kbx81/TubeClock/src/v1/Settings.h

//
// kbx81's tube clock settings class
// ---------------------------------------------------------------------------
// (c)2019 by kbx81. See LICENSE for details.
//
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
#pragma once

#include <cstdint>

#include "DateTime.h"

namespace kbxTubeClock {

class Settings {
 public:
  /// @brief Types of settings we keep
  ///
  enum Setting : uint8_t {
    SystemOptions = 0,
    BeepStates = 1,
    BlinkStates = 2,
    OnOffStates = 3,
    PMIndicatorRedValue = 4,
    PMIndicatorGreenValue = 5,
    PMIndicatorBlueValue = 6,
    TimeDisplayDuration = 7,
    DateDisplayDuration = 8,
    TemperatureDisplayDuration = 9,
    FadeDuration = 10,
    DstBeginMonth = 11,
    DstBeginDowOrdinal = 12,
    DstEndMonth = 13,
    DstEndDowOrdinal = 14,
    DstSwitchDayOfWeek = 15,
    DstSwitchHour = 16,
    EffectDuration = 17,
    EffectFrequency = 18,
    MinimumIntensity = 19,
    BeeperVolume = 20,
    TemperatureCalibrationSTM32 = 21,
    TemperatureCalibrationDS3234 = 22,
    TemperatureCalibrationDS1722 = 23,
    TemperatureCalibrationLM74 = 24,
    IdleTimeout = 25,
    DateFormat = 26,
    TimeZone = 27,
    ColonBehavior = 28,
    TimerResetValue = 29,
    DmxAddress = 30
  };

  /// @brief Settings we keep
  ///
  enum SystemOptionsBits : uint8_t {
    Display12Hour = 0,
    StatusLedAsAmPm = 1,
    HourlyChime = 2,
    DstEnable = 3,
    DisplayFahrenheit = 4,
    AutoAdjustIntensity = 5,
    StartupToToggle = 6,
    DmxExtended = 7,
    MSDsOff = 8,
    TriggerEffectOnRotate = 9
  };

  /// @brief Enums for time slots
  ///
  enum Slot : uint8_t {
    Slot1 = 0,
    Slot2 = 1,
    Slot3 = 2,
    Slot4 = 3,
    Slot5 = 4,
    Slot6 = 5,
    Slot7 = 6,
    Slot8 = 7,
    SlotDate = 8,
    SlotTemperature = 9,
    SlotTimer = 10,
    SlotMenu = 11,
    SlotSet = 12,
    SlotDmx = 13,
    SlotCalculated = 14
  };

 public:
  /// @brief Where settings will be written in FLASH
  /// @note This address is provided by the linker script (__settings_flash_start)
  ///       and is located at the end of flash memory to prevent conflicts with code
  ///
  static const uint32_t cSettingsFlashAddress;

  /// @brief How a setting's raw value is transformed for display/input
  ///
  enum class SettingTransform : uint8_t {
    None = 0,
    PlusOne,      ///< stored 0-based, displayed 1-based (e.g. DmxAddress: stored 0-504, shown 1-512)
    TimeZone,     ///< stored 0-112 (x15 min), displayed as signed ±HH:MM offset
    Calibration   ///< stored 0-198, displayed as signed offset from midpoint 99
  };

  /// @brief Describes valid range and display behavior of a setting
  ///
  struct SettingDescriptor {
    uint16_t        maxOrMask;   ///< max value for numerics; bitmask for bitfields
    uint8_t         minValue;    ///< minimum valid value (0 for most; 1 for months/ordinals)
    SettingTransform transform;  ///< how to interpret/display the value
  };

  /// @brief Descriptor for each setting (indexed by Setting enum)
  ///
  static const SettingDescriptor cSettingDescriptors[];

  /// @brief Midpoint value for signed temperature calibration encoding
  ///  stored = cCalibrationMidpoint + offsetCx10; offsetCx10 = stored - cCalibrationMidpoint
  static const int16_t cCalibrationMidpoint = 99;

  /// @brief Timezone encoding constants: stored value for UTC+0, and minutes per step
  ///  offsetMinutes = (stored - cTimeZoneUtcValue) * cTimeZoneStepMinutes
  static const uint16_t cTimeZoneUtcValue = 56;
  static const uint16_t cTimeZoneStepMinutes = 15;

  /// @brief Default constructor
  ///
  Settings();

  /// @brief Initialize settings
  ///
  void initialize();

  /// @brief Loads settings from FLASH
  /// @return true if success, false if failure & defaults were set
  ///
  bool loadFromFlash();

  /// @brief Loads settings from DS3234 SRAM; validates CRC
  /// @return true if DS3234 connected and CRC valid, false otherwise (defaults set)
  ///
  bool loadFromSram();

  /// @brief Saves current settings to DS3234 SRAM; no-op if DS3234 not connected
  /// @note Caller must ensure _crc is valid (i.e. call after saveToFlash())
  ///
  void saveToSram();

  /// @brief Invalidates the DS3234 SRAM copy of settings so it won't be used on next load; no-op if DS3234 not connected
  ///
  void invalidateSram();

  /// @brief Checks whether DS3234 SRAM contains valid settings (CRC check only, does not modify *this)
  /// @return true if DS3234 connected and SRAM CRC valid
  ///
  bool sramIsValid() const;

  /// @brief Saves settings to FLASH
  /// @return result of writeFlash()
  ///
  uint32_t saveToFlash();

  /// @brief Saves settings to FLASH only if they differ from the stored copy
  /// @return true on success (written or already up to date), false on write error
  ///
  bool saveToFlashIfChanged();

  /// @brief Returns a setting
  /// @return true if setting is enabled, false otherwise
  ///
  bool getSetting(const uint8_t setting, const uint8_t item);

  /// @brief Sets a setting
  ///
  void setSetting(const uint8_t setting, const uint8_t item, const bool state);

  /// @brief Returns all settings
  /// @return value of requested setting
  ///
  uint16_t getRawSetting(const uint8_t setting);

  /// @brief Sets all settings
  ///
  void setRawSetting(const uint8_t setting, const uint16_t value);

  /// @brief Get a time value stored in the settings
  ///
  DateTime getTime(const Slot setting);
  DateTime getTime(const uint8_t setting);

  /// @brief Set a time value in the settings
  ///
  void setTime(const Slot setting, const DateTime &time);
  void setTime(const uint8_t setting, const DateTime &time);

  /// @brief Returns the desired HV state based on the time
  /// @return true if HV should be on, false otherwise
  ///
  bool hvState();

 private:
  /// @brief array of values for various settings data
  ///
  uint16_t _setting[Setting::DmxAddress + 1];

  /// @brief array of stored times for the alarms and/or color changes
  ///
  DateTime _time[Slot::Slot8 + 1];

  /// @brief determines validity of Settings data after loading from FLASH
  ///
  uint32_t _crc;
};

}  // namespace kbxTubeClock
