kbx81/TubeClock/src/v1/Application.h

//
// kbx81's tube clock main application
// ---------------------------------------------------------------------------
// (c)2019 by kbx81. See LICENSE for details.
//
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
#pragma once

#include <cstdint>

#include "DateTime.h"
#include "Display.h"
#include "Settings.h"
#include "View.h"

namespace kbxTubeClock::Application {

/// @brief Application operating modes
///
enum OperatingMode : uint8_t {
  OperatingModeMainMenu,                  ///< Main Menu mode
  OperatingModeFixedDisplay,              ///< Fixed display mode
  OperatingModeToggleDisplay,             ///< Toggling display mode
  OperatingModeTimerCounter,              ///< Timer/counter mode
  OperatingModeDmx512Display,             ///< DMX-512 display mode
  OperatingModeSetClock,                  ///< Set timeclock mode
  OperatingModeSetDate,                   ///< Set date mode
  OperatingModeSetTimerResetValue,        ///< Set timer/counter reset value
  OperatingModeSystemStatusView,          ///< System status view mode
  OperatingModeSetSystemOptions,          ///< Set Binary/BCD and 24 hour bits mode
  OperatingModeSlotBeepConfig,            ///< Enable/Disable beeping (alarm) per-slot
  OperatingModeSlotBlinkConfig,           ///< Enable/Disable display blinking per-slot
  OperatingModeSlotOnOffConfig,           ///< Enable/Disable color change per-slot
  OperatingModeSlotPMIndicatorRGBConfig,  ///< Set RGB color for PM indicator
  OperatingModeSetDurationClock,          ///< Set duration of clock display mode
  OperatingModeSetDurationDate,           ///< Set duration of date display mode
  OperatingModeSetDurationTemp,           ///< Set duration of temperature display mode
  OperatingModeSetDurationFade,           ///< Set duration of fading for digits
  OperatingModeDstBeginMonth,             ///< Set first month of DST
  OperatingModeDstBeginDowOrdinal,        ///< Set which given day DST begins
  OperatingModeDstEndMonth,               ///< Set last month of DST
  OperatingModeDstEndDowOrdinal,          ///< Set which given day DST ends
  OperatingModeDstSwitchDayOfWeek,        ///< Set which day of week DST begins/ends
  OperatingModeDstSwitchHour,             ///< Set hour at which DST begins/ends
  OperatingModeSetEffectDuration,         ///< Set duration of display effects
  OperatingModeSetEffectFrequency,        ///< Set frequency of display effects
  OperatingModeSetMinimumIntensity,       ///< Set minimum display intensity
  OperatingModeSetBeeperVolume,           ///< Set Beeper Volume
  OperatingModeSetTempCalibration,        ///< Set temperature calibration
  OperatingModeSetIdleTimeout,            ///< Set idle timeout
  OperatingModeSetDateFormat,             ///< Set Date Format
  OperatingModeSetTimeZone,               ///< Set Time Zone
  OperatingModeSetColonBehavior,          ///< Set Colon/Seperator behavior (time display)
  OperatingModeSetDMX512Address,          ///< Set DMX-512 address mode
  OperatingModeSlot1Time,                 ///< Set slot 1 time mode
  OperatingModeSlot2Time,                 ///< Set slot 2 time mode
  OperatingModeSlot3Time,                 ///< Set slot 3 time mode
  OperatingModeSlot4Time,                 ///< Set slot 4 time mode
  OperatingModeSlot5Time,                 ///< Set slot 5 time mode
  OperatingModeSlot6Time,                 ///< Set slot 6 time mode
  OperatingModeSlot7Time,                 ///< Set slot 7 time mode
  OperatingModeSlot8Time,                 ///< Set slot 8 time mode
  OperatingModeTestDisplay                ///< Test display mode
};

/// @brief Enums for views
///
enum ViewEnum : uint8_t {
  MainMenuViewEnum = 0,
  TimeDateTempViewEnum = 1,
  TimerCounterViewEnum = 2,
  Dmx512ViewEnum = 3,
  SetTimeDateViewEnum = 4,
  SetBitsViewEnum = 5,
  SetValueViewEnum = 6,
  SystemStatusViewEnum = 7,
  TestDisplayEnum = 8
};

/// @brief Enums for views
///
enum ExternalControl : uint8_t { NoActiveExtControlEnum, SerialExtControlEnum, Dmx512ExtControlEnum };

/// @brief Number of seconds in a day
///
const uint16_t cSecondsInAnHour = 60 * 60;
const uint32_t cSecondsInADay = cSecondsInAnHour * 24;

// DST offset in seconds
//
static const int16_t cDstOffsetSeconds = 60 * 60;

/// @brief Common colors used throughout
///
extern const RgbLed red, green;

/// @brief Initialize the application
///
void initialize();

/// @brief Gets the application's date & time, adjusted for time zone and DST
///
DateTime dateTime();

/// @brief Set the date/time
///
void setDateTime(const DateTime &now);

/// @brief Returns the temperature based on hardware
///  (in fahrenheit if fahrenheit == true; in BCD if bcd == true)
int32_t temperature(const bool fahrenheit, const bool bcd = false);

/// @brief Returns the active sensor's temperature in tenths of degrees Celsius
///
int32_t temperatureCx10();

/// @brief Returns the temperature for a specific sensor type in tenths of degrees Celsius
///
int32_t temperatureCx10(Hardware::TempSensorType type);

/// @brief Returns true if any temperature reading has been updated since last call
///
bool temperatureUpdated();

/// @brief Get a mode's display number
/// @param mode Desired mode to get the display number for
///
uint8_t getModeDisplayNumber(OperatingMode mode);
uint8_t getModeDisplayNumber(uint8_t mode);

/// @brief Get application mode
///
OperatingMode getOperatingMode();

/// @brief Set new application mode
/// @param mode New application mode
///
void setOperatingMode(OperatingMode mode);

/// @brief Get view mode
///
ViewMode getViewMode();

/// @brief Set new view mode
/// @param mode New view mode
///
void setViewMode(ViewMode mode);

/// @brief Get view's related setting
/// @param mode Desired mode to get the related setting for
///
uint8_t getOperatingModeRelatedSetting(OperatingMode mode);

/// @brief Get external control status
///
ExternalControl getExternalControlState();

/// @brief Get a pointer to the application settings
///
Settings *getSettingsPtr();

/// @brief Refreshes hardware from current application settings
///
void refreshSettings();

/// @brief Notify the application that settings have been modified in-place via getSettingsPtr()
///
void notifySettingsChanged();

/// @brief Queue a serial notification that a numbered setting was changed via the local UI
/// @param settingNum The setting index that changed
///
void notifySettingChanged(uint8_t settingNum);

/// @brief Saves current settings to flash, skipping write if unchanged
/// @return true on success (saved or already up to date), false on write error
///
bool saveSettingsToFlash();

/// @brief Handles DST date/time computation; maintains clock's DST state machine.
///  Intended for tracking DST clock adjustments, not for arbitrary use!
///  To reset state machine, call with year != year provided when last called.
/// @param currentTime DateTime object to compute DST state for
/// @return true if DST is active based on passed DateTime object
bool isDst(const DateTime &currentTime);

/// @brief Returns state of automatic tube intensity adjustments
/// @return True if automatic tube intensity adjustment is enabled
bool getIntensityAutoAdjust();

/// @brief Enables/disables automatic adjusting of the tube display intensity based
///  on ambient light seen by the phototransistor
/// @param enable Enables automatic adjustments if true
/// @param quickAdjust Perform an immediate update of the intensity
void setIntensityAutoAdjust(const bool enable, const bool quickAdjust = false);

/// @brief Returns state of automatic status LED intensity adjustments
/// @return True if automatic LED intensity adjustment is enabled
bool getLedIntensityAutoAdjust();

/// @brief Enables/disables automatic adjusting of the status LED intensity based
///  on ambient light. Independent of tube auto-adjust.
/// @param enable Enables automatic LED adjustments if true
void setLedIntensityAutoAdjust(const bool enable);

/// @brief Returns the application's current display intensity
/// @return current display intensity (0-255)
uint8_t getIntensity();

/// @brief Returns the status LED's current master intensity
/// @return current LED intensity (0-255)
uint8_t getLedIntensity();

/// @brief Returns the application's startup settings load result
/// @return 0 = defaults used, 1 = loaded from flash, 2 = loaded from DS3234 SRAM
uint8_t getStartupSettingsLoadResult();

/// @brief Set the application's display intensity and disables automagic adjusting of the display intensity
/// @param intensity New display intensity (0-255)
///
void setIntensity(const uint8_t intensity);

/// @brief Set the status LED's master intensity independently of the nixie display intensity.
///        Disables LED auto-adjust; tube auto-adjust is unaffected.
/// @param intensity New LED intensity (0-255)
///
void setLedIntensity(const uint8_t intensity);

/// @brief Refreshs master display intensity. Call at fixed intervals.
///
void tick();

/// @brief The main loop of the application.
///
__attribute__((noreturn)) void loop();

}  // namespace kbxTubeClock::Application
