kbx81/TubeClock/src/v1/RgbLed.cpp

//
// kbx81's RGB LED Library
// ---------------------------------------------------------------------------
// (c)2017 by kbx81. See LICENSE for details.
//
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

#include "RgbLed.h"

/// @mainpage
///
/// @section intro_sec Introduction
///
/// This library contains a class to manage the Binary Clock's RGB LEDs.
///
/// @section requirements_sec Requirements
///
/// This library is written in a manner so as to be compatible on a range of
/// CPUs/MCUs. It has been tested on Arduino and STM32F0 platforms. It requires
/// a modern C++ compiler (C++11).
///
/// @section classes_sec Classes
///
/// There is only the RgbLed::RgbLed class. Read the documentation of this class
/// for all details.
///

namespace kbxTubeClock {

/// 4096-step (12 bit) brightness table: gamma = 2.2
///
const uint16_t RgbLed::cGammaTable[4096] = {
    0,    0,    0,    0,    0,    0,    0,    0,    0,    0,    0,    0,    0,    0,    0,    0,    0,    0,    0,
    0,    0,    0,    0,    0,    0,    0,    0,    0,    0,    0,    0,    0,    0,    0,    0,    0,    0,    0,
    0,    0,    0,    0,    0,    0,    0,    0,    0,    0,    0,    0,    0,    0,    0,    0,    0,    0,    0,
    0,    0,    0,    0,    0,    0,    0,    0,    0,    0,    0,    1,    1,    1,    1,    1,    1,    1,    1,
    1,    1,    1,    1,    1,    1,    1,    1,    1,    1,    1,    1,    1,    1,    1,    1,    1,    1,    1,
    1,    1,    1,    1,    1,    1,    1,    1,    1,    1,    1,    1,    1,    1,    1,    1,    1,    1,    2,
    2,    2,    2,    2,    2,    2,    2,    2,    2,    2,    2,    2,    2,    2,    2,    2,    2,    2,    2,
    2,    2,    2,    2,    2,    2,    2,    2,    2,    3,    3,    3,    3,    3,    3,    3,    3,    3,    3,
    3,    3,    3,    3,    3,    3,    3,    3,    3,    3,    3,    3,    3,    3,    4,    4,    4,    4,    4,
    4,    4,    4,    4,    4,    4,    4,    4,    4,    4,    4,    4,    4,    4,    4,    5,    5,    5,    5,
    5,    5,    5,    5,    5,    5,    5,    5,    5,    5,    5,    5,    5,    6,    6,    6,    6,    6,    6,
    6,    6,    6,    6,    6,    6,    6,    6,    6,    6,    7,    7,    7,    7,    7,    7,    7,    7,    7,
    7,    7,    7,    7,    7,    7,    8,    8,    8,    8,    8,    8,    8,    8,    8,    8,    8,    8,    8,
    8,    9,    9,    9,    9,    9,    9,    9,    9,    9,    9,    9,    9,    10,   10,   10,   10,   10,   10,
    10,   10,   10,   10,   10,   10,   11,   11,   11,   11,   11,   11,   11,   11,   11,   11,   11,   11,   12,
    12,   12,   12,   12,   12,   12,   12,   12,   12,   12,   13,   13,   13,   13,   13,   13,   13,   13,   13,
    13,   14,   14,   14,   14,   14,   14,   14,   14,   14,   14,   15,   15,   15,   15,   15,   15,   15,   15,
    15,   15,   16,   16,   16,   16,   16,   16,   16,   16,   16,   17,   17,   17,   17,   17,   17,   17,   17,
    17,   17,   18,   18,   18,   18,   18,   18,   18,   18,   19,   19,   19,   19,   19,   19,   19,   19,   19,
    20,   20,   20,   20,   20,   20,   20,   20,   21,   21,   21,   21,   21,   21,   21,   21,   22,   22,   22,
    22,   22,   22,   22,   22,   23,   23,   23,   23,   23,   23,   23,   23,   24,   24,   24,   24,   24,   24,
    24,   25,   25,   25,   25,   25,   25,   25,   25,   26,   26,   26,   26,   26,   26,   26,   27,   27,   27,
    27,   27,   27,   27,   28,   28,   28,   28,   28,   28,   28,   29,   29,   29,   29,   29,   29,   30,   30,
    30,   30,   30,   30,   30,   31,   31,   31,   31,   31,   31,   31,   32,   32,   32,   32,   32,   32,   33,
    33,   33,   33,   33,   33,   34,   34,   34,   34,   34,   34,   34,   35,   35,   35,   35,   35,   35,   36,
    36,   36,   36,   36,   36,   37,   37,   37,   37,   37,   37,   38,   38,   38,   38,   38,   39,   39,   39,
    39,   39,   39,   40,   40,   40,   40,   40,   40,   41,   41,   41,   41,   41,   42,   42,   42,   42,   42,
    42,   43,   43,   43,   43,   43,   44,   44,   44,   44,   44,   44,   45,   45,   45,   45,   45,   46,   46,
    46,   46,   46,   47,   47,   47,   47,   47,   47,   48,   48,   48,   48,   48,   49,   49,   49,   49,   49,
    50,   50,   50,   50,   50,   51,   51,   51,   51,   51,   52,   52,   52,   52,   52,   53,   53,   53,   53,
    53,   54,   54,   54,   54,   55,   55,   55,   55,   55,   56,   56,   56,   56,   56,   57,   57,   57,   57,
    57,   58,   58,   58,   58,   59,   59,   59,   59,   59,   60,   60,   60,   60,   61,   61,   61,   61,   61,
    62,   62,   62,   62,   63,   63,   63,   63,   63,   64,   64,   64,   64,   65,   65,   65,   65,   65,   66,
    66,   66,   66,   67,   67,   67,   67,   68,   68,   68,   68,   69,   69,   69,   69,   69,   70,   70,   70,
    70,   71,   71,   71,   71,   72,   72,   72,   72,   73,   73,   73,   73,   74,   74,   74,   74,   75,   75,
    75,   75,   76,   76,   76,   76,   77,   77,   77,   77,   78,   78,   78,   78,   79,   79,   79,   79,   80,
    80,   80,   80,   81,   81,   81,   81,   82,   82,   82,   82,   83,   83,   83,   84,   84,   84,   84,   85,
    85,   85,   85,   86,   86,   86,   86,   87,   87,   87,   88,   88,   88,   88,   89,   89,   89,   89,   90,
    90,   90,   91,   91,   91,   91,   92,   92,   92,   92,   93,   93,   93,   94,   94,   94,   94,   95,   95,
    95,   96,   96,   96,   96,   97,   97,   97,   98,   98,   98,   98,   99,   99,   99,   100,  100,  100,  100,
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

RgbLed::RgbLed(const uint16_t red, const uint16_t green, const uint16_t blue, const uint32_t duration)
    : _duration(duration), _red(red), _green(green), _blue(blue) {}

bool RgbLed::operator==(const RgbLed &other) const {
  return _red == other._red && _green == other._green && _blue == other._blue && _duration == other._duration &&
         _intensity == other._intensity;
}

bool RgbLed::operator!=(const RgbLed &other) const { return !(*this == other); }

void RgbLed::setIntensity(const uint8_t intensity) { _intensity = intensity; }

void RgbLed::setRed(const uint16_t intensityRed) { _red = intensityRed; }

void RgbLed::setGreen(const uint16_t intensityGreen) { _green = intensityGreen; }

void RgbLed::setBlue(const uint16_t intensityBlue) { _blue = intensityBlue; }

void RgbLed::setRGB(const uint16_t intensityRed, const uint16_t intensityGreen, const uint16_t intensityBlue) {
  _red = intensityRed;
  _green = intensityGreen;
  _blue = intensityBlue;
}

void RgbLed::setOff() {
  _red = 0;
  _green = 0;
  _blue = 0;
}

void RgbLed::setDuration(const uint32_t duration) { _duration = duration; }

uint8_t RgbLed::getIntensity() const { return _intensity; }

uint16_t RgbLed::getRed() const { return _red; }

uint16_t RgbLed::getGreen() const { return _green; }

uint16_t RgbLed::getBlue() const { return _blue; }

uint32_t RgbLed::getDuration() const { return _duration; }

void RgbLed::adjustIntensity(uint16_t scaleFactor) {
  uint32_t top;

  top = _red * scaleFactor;
  _red = top >> 16;

  top = _green * scaleFactor;
  _green = top >> 16;

  top = _blue * scaleFactor;
  _blue = top >> 16;
}

void RgbLed::gammaCorrect12bit() {
  const uint16_t mask = 0xfff;  // 12 bits

  _red = RgbLed::cGammaTable[_red & mask];
  _green = RgbLed::cGammaTable[_green & mask];
  _blue = RgbLed::cGammaTable[_blue & mask];
}

}  // namespace kbxTubeClock
