kbx81/TubeClock/src/v1/GpsReceiver.cpp

//
// kbx81's tube clock GpsReceiver Library
// ---------------------------------------------------------------------------
// (c)2019 by kbx81. See LICENSE for details.
//
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
#include <cstring>

#include "Hardware.h"
#include "GpsReceiver.h"

#if HARDWARE_VERSION == 1
#include "Hardware_v1.h"
#else
#error HARDWARE_VERSION must be defined with a value of 1
#endif

namespace kbxTubeClock::GpsReceiver {

/// @brief GPS Receiver state machine states
///
enum GpsRxState : uint8_t {
  GpsRxIdle = 0,
  GpsRxGettingHeader = 1,
  GpsRxNmeaHeaderValid = 2,
  GpsRxTimeReceived = 3,
  GpsRxTimeCompleted = 4,
  GpsRxWaitForDate = 5,
  GpsRxDate = 6,
  GpsRxNumSatellites = 7,
  GpsRxWaitForChecksum = 8,  // GPRMC: eat trailing fields until '*'
  GpsRxChecksumHigh = 9,     // read high hex nibble of checksum
  GpsRxChecksumLow = 10      // read low hex nibble, validate, commit
};

/// @brief GPS Receiver sentence type
///
enum GpsRxType : uint8_t { GpsRMC = 0, GpsGSV = 1 };

// the header on the string we expect to parse
// $GPRMC,000012.800,V,,,,,0.00,0.00,060180,,,N*49
// $GPRMC,230912.000,A,4055.5342,N,08341.7690,W,1.24,299.67,070519,,,D*71
//
static const char cGpsParseStrGSV[] = "$GPGSV,";
static const char cGpsParseStrRMC[] = "$GPRMC,";

// the length of the string we expect to parse
//
static const uint8_t cGpsNmeaHeaderLength = 7;

// the length of the date and time strings we expect to receive
//
static const uint8_t cGpsDateTimeLength = 6;

// the number of commas seen before we receive the date
//
static const uint8_t cGpsPreDateCommaCount = 7;

// the number of commas seen before we receive the number of satellites
//
static const uint8_t cGpsPreNumSatellitesCommaCount = 2;

// tracks the receiver state machine's state
//
static GpsRxState _rxState = GpsRxState::GpsRxIdle;

// tracks the sentence type the receiver is sending
//
static GpsRxType _rxType = GpsRxType::GpsRMC;

// a counter for incoming characters
//
static uint8_t _rxCharCount = 0;

// indicates the validity of the incoming data
//
static char _rxValidChar = 0;

// buffer for sentence header (7 bytes, .bss — init value irrelevant, ISR overwrites all bytes)
//
static char _rxHeaderChar[7];

// date and time incoming character buffers
//
static char _rxDateChar[6];
static char _rxTimeChar[6];

// number of  minutes added to GPS time to compute local time
//
static int16_t _timeZoneOffsetInMinutes = 0;

// the current date and time received from the GPS
//
static DateTime _gpsTime;

// the current number of satellites seen by the GPS
//
static uint8_t _numSatellites = 0;

// NMEA checksum state: running XOR accumulator and received checksum byte
//
static uint8_t _checksum = 0;
static uint8_t _checksumRx = 0;

// cached Usart pointer for GPS USART
//
static Usart *_gpsUsart = nullptr;

// Decode one ASCII hex character to its 4-bit value
//
static uint8_t _hexNibble(const uint8_t c) {
  return (c >= 'A') ? (c - 'A' + 10) : (c - '0');
}

void initialize() {
  _gpsUsart = Hardware::getUsart(0);  // USART1
}

/// @brief Updates our DateTime object based on the receive buffers
///
void _rxRmcComplete() {
  uint16_t year = 2000;
  uint8_t month = 0, day = 0, hour = 0, minute = 0, second = 0;

  day = ((_rxDateChar[0] - '0') * 10) + (_rxDateChar[1] - '0');
  month = ((_rxDateChar[2] - '0') * 10) + (_rxDateChar[3] - '0');
  year += ((_rxDateChar[4] - '0') * 10) + (_rxDateChar[5] - '0');

  hour = ((_rxTimeChar[0] - '0') * 10) + (_rxTimeChar[1] - '0');
  minute = ((_rxTimeChar[2] - '0') * 10) + (_rxTimeChar[3] - '0');
  second = ((_rxTimeChar[4] - '0') * 10) + (_rxTimeChar[5] - '0');

  _gpsTime.setDate(year, month, day);
  _gpsTime.setTime(hour, minute, second);
}

bool isConnected() { return ((_rxValidChar == 'A') || (_rxValidChar == 'V')); }

bool isValid() { return (_rxValidChar == 'A'); }

DateTime getDateTime() { return _gpsTime; }

DateTime getLocalDateTime() { return _gpsTime.addSeconds(_timeZoneOffsetInMinutes * 60); }

uint8_t getSatellitesInView() { return _numSatellites; }

void setTimeZone(const int16_t offsetInMinutes) { _timeZoneOffsetInMinutes = offsetInMinutes; }

void rxIsr() {
  if (_gpsUsart == nullptr || !_gpsUsart->rxReady()) {
    return;
  }

  uint8_t rxChar = _gpsUsart->readByte();

  // Accumulate XOR checksum for all bytes between '$' (exclusive) and '*' (exclusive).
  // States GpsRxGettingHeader through GpsRxDate cover the header + all RMC payload fields.
  // GpsRxWaitForChecksum handles bytes between the date field and '*' inline.
  if (_rxState >= GpsRxState::GpsRxGettingHeader && _rxState <= GpsRxState::GpsRxDate) {
    _checksum ^= rxChar;
  }

  switch (_rxState) {
    // at this point, we've seen the "$GPRMC," characters and can expect the time or a sentence count next
    case GpsRxState::GpsRxNmeaHeaderValid:
      if (_rxType == GpsRxType::GpsRMC) {
        _rxTimeChar[_rxCharCount] = rxChar;

        if (++_rxCharCount >= cGpsDateTimeLength) {
          _rxState = GpsRxState::GpsRxTimeReceived;
          _rxCharCount = 0;
        }
      } else if (_rxType == GpsRxType::GpsGSV) {
        if (rxChar == ',') {
          if (++_rxCharCount >= cGpsPreNumSatellitesCommaCount) {
            _rxState = GpsRxState::GpsRxNumSatellites;
            _rxCharCount = 0;
          }
        }
      }
      break;

    // the time has been received, here we'll just eat a comma and move along
    case GpsRxState::GpsRxTimeReceived:
      if (rxChar == ',') {
        _rxState = GpsRxState::GpsRxTimeCompleted;
      }
      break;

    // now we should see either an 'A' or a 'V' indicating validity
    case GpsRxState::GpsRxTimeCompleted:
      if ((rxChar == 'A') || (rxChar == 'V')) {
        _rxValidChar = rxChar;
        _rxState = GpsRxState::GpsRxWaitForDate;
      } else {
        _rxState = GpsRxState::GpsRxIdle;
      }
      break;

    // the validity has been received, now we'll eat more commas
    case GpsRxState::GpsRxWaitForDate:
      if (rxChar == ',') {
        if (++_rxCharCount >= cGpsPreDateCommaCount) {
          _rxState = GpsRxState::GpsRxDate;
          _rxCharCount = 0;
        }
      }
      break;

    // finally we get the date; defer commit until checksum validates
    case GpsRxState::GpsRxDate:
      _rxDateChar[_rxCharCount] = rxChar;

      if (++_rxCharCount >= cGpsDateTimeLength) {
        _rxState = GpsRxState::GpsRxWaitForChecksum;
        _rxCharCount = 0;
      }
      break;

    // eat trailing GPRMC fields until '*', accumulating them into the checksum
    case GpsRxState::GpsRxWaitForChecksum:
      if (rxChar == '*') {
        _rxState = GpsRxState::GpsRxChecksumHigh;
      } else {
        _checksum ^= rxChar;
      }
      break;

    // read high hex nibble of received checksum
    case GpsRxState::GpsRxChecksumHigh:
      _checksumRx = _hexNibble(rxChar) << 4;
      _rxState = GpsRxState::GpsRxChecksumLow;
      break;

    // read low hex nibble, validate, and commit if checksum matches
    case GpsRxState::GpsRxChecksumLow:
      _checksumRx |= _hexNibble(rxChar);
      if (_checksumRx == _checksum) {
        _rxRmcComplete();
      }
      _rxState = GpsRxState::GpsRxIdle;
      _rxCharCount = 0;
      break;

    // read in the two-digit number of satellites — accumulate directly to avoid buffer
    case GpsRxState::GpsRxNumSatellites:
      if (_rxCharCount == 0) {
        _numSatellites = (rxChar - '0') * 10;
        ++_rxCharCount;
      } else {
        _numSatellites += rxChar - '0';
        _rxState = GpsRxState::GpsRxIdle;
        _rxCharCount = 0;
      }
      break;

    // the first big step...read in up to cGpsNmeaHeaderLength header characters
    case GpsRxState::GpsRxGettingHeader:
      _rxHeaderChar[_rxCharCount] = rxChar;
      // if we've received enough characters, compare the strings for validity
      if (++_rxCharCount >= cGpsNmeaHeaderLength) {
        if (memcmp(cGpsParseStrGSV, _rxHeaderChar, cGpsNmeaHeaderLength) == 0) {
          _rxState = GpsRxState::GpsRxNmeaHeaderValid;
          _rxType = GpsRxType::GpsGSV;
          _rxCharCount = 0;
        } else if (memcmp(cGpsParseStrRMC, _rxHeaderChar, cGpsNmeaHeaderLength) == 0) {
          _rxState = GpsRxState::GpsRxNmeaHeaderValid;
          _rxType = GpsRxType::GpsRMC;
          _rxCharCount = 0;
        } else  // nothing matched so just start over
        {
          _rxState = GpsRxState::GpsRxIdle;
          _rxCharCount = 0;
        }
      }
      break;

    // it starts here...we patiently wait for that money header tag! ('$')
    default:
      if (rxChar == '$') {
        _checksum = 0;  // reset XOR accumulator for new sentence ('$' itself is not checksummed)
        _rxHeaderChar[_rxCharCount++] = rxChar;
        _rxState = GpsRxState::GpsRxGettingHeader;
      }
  }
}

}  // namespace kbxTubeClock::GpsReceiver
