kbx81/TubeClock/src/v1/SystemStatusView.cpp

//
// kbx81's tube clock system status view class
// ---------------------------------------------------------------------------
// (c)2019 by kbx81. See LICENSE for details.
//
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
#include "Application.h"
#include "BuildInfo.h"
#include "DateTime.h"
#include "DisplayManager.h"
#include "GpsReceiver.h"
#include "Hardware.h"
#include "Settings.h"
#include "SystemStatusView.h"

#if HARDWARE_VERSION == 1
#include "Hardware_v1.h"
#else
#error HARDWARE_VERSION must be defined with a value of 1
#endif

namespace kbxTubeClock {

SystemStatusView::SystemStatusView() : _selectedView(0) {}

void SystemStatusView::enter(const Settings::SettingDescriptor * /*descriptor*/, uint8_t /*relatedSetting*/,
                             uint8_t /*numSettings*/) {
  DisplayManager::setStatusLedAutoRefreshing(true);
}

bool SystemStatusView::keyHandler(Keys::Key key) {
  bool tick = false;

  if (key == Keys::Key::A) {
  }

  if (key == Keys::Key::B) {
  }

  if (key == Keys::Key::C) {
    if (_selectedView == DisplayItem::TubeLifetime) {
      Hardware::onTimeSecondsReset();
    }
  }

  if (key == Keys::Key::D) {
    if (--_selectedView < 0) {
      _selectedView = static_cast<uint8_t>(DisplayItem::BuildNumber);
    }
    Application::setViewMode(static_cast<ViewMode>(_selectedView));
    tick = true;
  }

  if (key == Keys::Key::U) {
    if (++_selectedView > static_cast<uint8_t>(DisplayItem::BuildNumber)) {
      _selectedView = 0;
    }
    Application::setViewMode(static_cast<ViewMode>(_selectedView));
    tick = true;
  }

  if (key == Keys::Key::E) {
    Application::setOperatingMode(Application::OperatingMode::OperatingModeMainMenu);
  }

  return tick;
}

void SystemStatusView::loop() {
  _selectedView = static_cast<int8_t>(Application::getViewMode());

  auto voltageBatt = Hardware::voltageBatt(), voltageVddA = Hardware::voltageVddA();
  auto rtcStartupResult = Hardware::getRTCStartupResult();
  uint8_t settingsLoadResult = Application::getStartupSettingsLoadResult();
  uint32_t dotsBitmap = 0b0011;
  uint8_t tubeIntensityBitmap = 0b111111;
  RgbLed statusLed;
  NixieGlyph dot(NixieGlyph::cGlyphMaximumIntensity);
  Display tcDisp;

  switch (_selectedView) {
    case DisplayItem::TubeLifetime:
      dotsBitmap = 0;

      if (Hardware::onTimeSeconds() < Application::cSecondsInAnHour) {
        tcDisp.setDisplayFromWord(Hardware::onTimeSeconds());
      } else {
        tcDisp.setDisplayFromWord(Hardware::onTimeSeconds() / Application::cSecondsInAnHour);
      }
      // If the PPS trigger is selected, light the status LED when the PPS signal is high
      if (Hardware::getPeripheralRefreshTrigger() == Hardware::PeripheralRefreshTrigger::PpsExti) {
        if (Hardware::getPpsInputState() == true) {
          Settings *pSettings = Application::getSettingsPtr();
          statusLed.setRGB(pSettings->getRawSetting(Settings::Setting::PMIndicatorRedValue),
                           pSettings->getRawSetting(Settings::Setting::PMIndicatorGreenValue),
                           pSettings->getRawSetting(Settings::Setting::PMIndicatorBlueValue));
        }
      }
      break;

    case DisplayItem::GpsStatus:
      if (GpsReceiver::isConnected() == true) {
        tubeIntensityBitmap = 0b110011;
        tcDisp.setDisplayFromWord(GpsReceiver::getSatellitesInView());
        if (GpsReceiver::isValid() == true) {
          statusLed = Application::green;
        } else {
          statusLed = Application::red;
        }
      } else {
        tubeIntensityBitmap = 0b110000;
      }
      break;

    case DisplayItem::StatusDS3234:
      tubeIntensityBitmap = 0b111111;
      tcDisp.setTubeToValue(0, 4);
      tcDisp.setTubeToValue(1, 3);
      tcDisp.setTubeToValue(2, 2);
      tcDisp.setTubeToValue(3, 3);
      if (Hardware::getRTCType() == Hardware::RtcType::DS323x) {
        statusLed = Application::green;
      } else {
        statusLed = Application::red;
      }
      break;

    case DisplayItem::StatusDS1722:
      tubeIntensityBitmap = 0b111111;
      tcDisp.setTubeToValue(0, 2);
      tcDisp.setTubeToValue(1, 2);
      tcDisp.setTubeToValue(2, 7);
      tcDisp.setTubeToValue(3, 1);
      if (Hardware::isTempSensorDetected(Hardware::TempSensorType::DS1722)) {
        statusLed = Application::green;
      } else {
        statusLed = Application::red;
      }
      break;

    case DisplayItem::StatusLM74:
      tubeIntensityBitmap = 0b110011;
      tcDisp.setTubeToValue(0, 4);
      tcDisp.setTubeToValue(1, 7);
      if (Hardware::isTempSensorDetected(Hardware::TempSensorType::LM74)) {
        statusLed = Application::green;
      } else {
        statusLed = Application::red;
      }
      break;

    case DisplayItem::VoltageVddA:
      dotsBitmap = 0b1000011;
      tcDisp.setDisplayFromWord(voltageVddA);
      break;

    case DisplayItem::VoltageBattery:
      dotsBitmap = 0b1000011;
      tcDisp.setDisplayFromWord(voltageBatt);
      break;

    case DisplayItem::StartupResult:
      tubeIntensityBitmap = 0b110101;
      tcDisp.setTubeToValue(0, settingsLoadResult);
      tcDisp.setTubeToValue(2, static_cast<uint8_t>(rtcStartupResult));
      break;

    case DisplayItem::FirmwareVersion:
      // kFirmwareVersion is always "YY.MM.PP" — all components zero-padded to 2 digits.
      dotsBitmap = 0b1010;                                  // lower dots only
      tcDisp.setTubeToValue(5, kFirmwareVersion[0] - '0');  // year tens
      tcDisp.setTubeToValue(4, kFirmwareVersion[1] - '0');  // year ones
      tcDisp.setTubeToValue(3, kFirmwareVersion[3] - '0');  // month tens
      tcDisp.setTubeToValue(2, kFirmwareVersion[4] - '0');  // month ones
      tcDisp.setTubeToValue(1, kFirmwareVersion[6] - '0');  // patch tens
      tcDisp.setTubeToValue(0, kFirmwareVersion[7] - '0');  // patch ones
      break;

    case DisplayItem::BuildNumber:
      tcDisp.setDisplayFromWord(kFirmwareBuild);
      for (uint8_t i = tcDisp.cTubeCount - 1; i > 0; i--) {
        if (tcDisp.getTubeValue(i) == 0) {
          tubeIntensityBitmap &= ~(1 << i);  // blank tube if digit is 0
        } else {
          break;  // stop blanking tubes once we hit a non-zero digit
        }
      }
      tubeIntensityBitmap |= 0b110000;
      break;

    default:
      break;
  }

  if (_selectedView != DisplayItem::TubeLifetime && _selectedView != DisplayItem::FirmwareVersion) {
    tcDisp.setTubeToValue(4, _selectedView);
  }
  tcDisp.setTubeIntensities(NixieGlyph::cGlyphMaximumIntensity, 0, tubeIntensityBitmap);
  tcDisp.setDots(dotsBitmap, dot, true);
  DisplayManager::setStatusLedIntensity(Application::getIntensity());
  DisplayManager::writeDisplay(tcDisp, statusLed);
}

}  // namespace kbxTubeClock
