kbx81/TubeClock/src/v1/DisplayManager.h

//
// kbx81's tube clock DisplayManager Library
// ---------------------------------------------------------------------------
// (c)2019 by kbx81. See LICENSE for details.
//
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
#pragma once

#include <cstdint>

#include "Display.h"
#include "RgbLed.h"

/// @brief kbx Binary Clock DisplayManager
///
namespace kbxTubeClock::DisplayManager {

/// @brief Initialize DisplayManager
///
void initialize();

/// @brief Refreshes intensities of tubes that are changing intensity levels due to (an) active crossfade(s)
/// @note This function is now a no-op. Refresh is integrated into tick() for better performance.
///
void refresh();

/// @brief Triggers a refresh of tubes intensities next time refresh() is called
///
void tick();

/// @brief Triggers a refresh of the tube PWM states and refreshes the drivers
///
void tickPWM();

/// @brief Enables/Disables control of the status LED by refresh() (above)
/// @param autoRefreshEnabled New state for status LED auto-refreshing
///
void setStatusLedAutoRefreshing(const bool autoRefreshEnabled);

/// @brief Returns the current "master" intensity of the display
/// @return Current master intensity (0-255)
///
uint8_t getMasterIntensity();

/// @brief Sets the "master" intensity of the display (0-255)
/// @param intensity New master intensity for display. Display is updated at next tick()
void setMasterIntensity(const uint8_t intensity);

/// @brief Get the state of display blanking
/// @return true if display is blank/off
///
bool getDisplayBlanking();

/// @brief Returns true if a blink() animation is currently in progress
///
bool isBlinkActive();

/// @brief Blank the display
/// @param blank Display is blank (off) if true
///
void setDisplayBlanking(const bool blank);

/// @brief Blinks the display count times as a non-blocking animation.
///  The animation is driven by tick() and completes asynchronously (~100ms per blink).
/// @param count Number of blinks (default 2)
///
void blink(uint8_t count = 2);

/// @brief Writes the passed display into the display buffer. Tubes will fade
///  to the intensities in the new display at the specified rates.
/// @param display Display to be written
/// @param statusLed Status LED state
///
void writeDisplay(const Display &display);
void writeDisplay(const Display &display, const RgbLed &statusLed);

/// @brief Sets the status LED's color and intensity from the passed RgbLed object.
///  Any change to color or intensity triggers a hardware update.
/// @param statusLed New status LED state (color + intensity both applied)
///
void writeStatusLed(const RgbLed &statusLed);

/// @brief Sets the status LED's master intensity (0–255) without changing its color
/// @param intensity New master intensity
///
void setStatusLedIntensity(uint8_t intensity);

/// @brief Returns the current status LED state as stored in the DisplayManager
/// @return Current RgbLed value (includes master intensity)
///
RgbLed getStatusLed();

/// @brief Returns true if the stored status LED color is already gamma-corrected
/// @return true if gamma correction is bypassed in refresh(), false if applied
///
bool getStatusLedPreCorrected();

/// @brief Sets whether the stored status LED color should bypass gamma correction
/// @param preCorrect true = skip gammaCorrect12bit() in refresh(); false = apply it (default)
///
void setStatusLedPreCorrected(bool preCorrect);

}  // namespace kbxTubeClock::DisplayManager
