kbx81/TubeClock/src/v1/TimeDateTempView.h

//
// kbx81's tube clock TestDisplayView class
// ---------------------------------------------------------------------------
// (c)2019 by kbx81. See LICENSE for details.
//
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
#pragma once

#include <cstdint>

#include "Application.h"
#include "DateTime.h"
#include "Display.h"
#include "Settings.h"
#include "View.h"

namespace kbxTubeClock {

class TimeDateTempView : public View {
  enum FixedDisplayItem : uint8_t {
    Time = ViewMode::ViewMode0,
    TimeSeconds = ViewMode::ViewMode1,
    Date = ViewMode::ViewMode2,
    Temperature = ViewMode::ViewMode3
  };

  // The view which displays either the date, time, temperature, or a rotation
  //
 public:  // Implement the TimeDateTempView class
  TimeDateTempView();
  virtual void enter(const Settings::SettingDescriptor* descriptor,
                     uint8_t relatedSetting, uint8_t numSettings = 1) override;
  virtual bool keyHandler(Keys::Key key) override;
  virtual void loop() override;

 private:
  // returns the appropriate dateTimeDisplaySelection for setDisplayFromDateTime
  //
  Display::dateTimeDisplaySelection _getDisplaySelection(const FixedDisplayItem item);

  // sets a display object based on the current view mode
  //
  void _setDisplay(Display *display, const FixedDisplayItem item);

  // sets the desired status LED color based on AM/PM and user settings
  //
  void _setStatusLed(const RgbLed &statusLed);

  // returns the display duration setting for a given display item
  //
  uint16_t _getItemDuration(const FixedDisplayItem item);

  // returns a bitmap of dot states for use during time display
  //
  uint16_t _getDotsBitmap();

 private:
  // amount by which we increment/decrement the intensity when manually adjusting
  //
  static const uint8_t cIntensityAdjustmentIncrement;

  // temperature
  //
  int32_t _currentTemperature;

  // date & time
  //
  DateTime _currentTime;

  // current status LED color (used for AM/PM indication, when enabled)
  //
  RgbLed _statusLed;

  // seconds elapsed since the last display animation
  //
  uint16_t _animationElapsed;

  // seconds elapsed since the last display switch
  //
  uint16_t _switchElapsed;

  // the main application's mode
  //
  Application::OperatingMode _mode;

  // tracks the display item from the previous loop to detect external view mode changes
  //
  FixedDisplayItem _prevDisplayItem;

  // tracks previous pmOn state to detect transitions and manage LED auto-adjust
  //
  bool _prevPmOn = false;
  bool _pmOnStale = true;  // true forces LED auto-adjust resync on next loop()

  // true if status LED should be refreshed by the next loop iteration
  //
  bool _refreshStatusLed = false;
};

}  // namespace kbxTubeClock
