kbx81/TubeClock/src/v1/NixieTube.cpp

//
// kbx81's Nixie Tube Library
// ---------------------------------------------------------------------------
// (c)2019 by kbx81. See LICENSE for details.
//
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

#include "NixieGlyph.h"
#include "NixieTube.h"

/// @mainpage
///
/// @section intro_sec Introduction
///
/// This library contains a class to manage the Tube Clock's glyphs.
///
/// @section requirements_sec Requirements
///
/// This library is written in a manner so as to be compatible on a range of
/// CPUs/MCUs. It has been tested on Arduino and STM32F0 platforms. It requires
/// a modern C++ compiler (C++11).
///
/// @section classes_sec Classes
///
/// There is only the NixieTube::NixieTube class. Read the documentation of
/// this class for all details.
///

namespace kbxTubeClock {

NixieTube::NixieTube(const uint8_t glyph, const uint8_t intensity, const uint32_t duration)
    : _duration(duration), _intensity(), _activeGlyph(glyph) {
  for (uint8_t i = 0; i < cGlyphsPerTube; i++) {
    _intensity[i] = 0;
  }

  if (glyph < cGlyphsPerTube) {
    _intensity[glyph] = intensity;
  } else {
    _activeGlyph = 0;
    _intensity[_activeGlyph] = intensity;
  }
}

bool NixieTube::operator==(const NixieTube &other) const {
  for (uint8_t i = 0; i < cGlyphsPerTube; i++) {
    if (_intensity[i] != other._intensity[i]) {
      return false;
    }
  }

  return _activeGlyph == other._activeGlyph && _duration == other._duration;
}

bool NixieTube::operator!=(const NixieTube &other) const {
  for (uint8_t i = 0; i < cGlyphsPerTube; i++) {
    if (_intensity[i] != other._intensity[i]) {
      return true;
    }
  }

  return _activeGlyph != other._activeGlyph || _duration != other._duration;
}

void NixieTube::setGlyph(const uint8_t glyph) {
  if ((glyph < cGlyphsPerTube) && (glyph != _activeGlyph)) {
    _intensity[glyph] = _intensity[_activeGlyph];  // new glyph on
    _intensity[_activeGlyph] = 0;                  // previous glyph off
    _activeGlyph = glyph;                          // update what's active
  }
}

void NixieTube::setIntensity(const uint8_t intensity) { setIntensity(_activeGlyph, intensity); }

void NixieTube::setIntensity(const uint8_t glyph, const uint8_t intensity) {
  if (glyph < cGlyphsPerTube) {
    _intensity[glyph] = intensity;
  }
}

void NixieTube::setDuration(const uint32_t duration) { _duration = duration; }

void NixieTube::setOff() {
  for (uint8_t glyph = 0; glyph < cGlyphsPerTube; glyph++) {
    _intensity[glyph] = 0;
  }
}

uint8_t NixieTube::getGlyph() const { return _activeGlyph; }

NixieGlyph NixieTube::getGlyphRaw() const { return getGlyphRaw(_activeGlyph); }

NixieGlyph NixieTube::getGlyphRaw(const uint8_t glyph) const {
  if (glyph < cGlyphsPerTube) {
    return NixieGlyph(_intensity[glyph], _duration);
  }
  return NixieGlyph(_intensity[_activeGlyph], _duration);
}

uint8_t NixieTube::getIntensity() const { return _intensity[_activeGlyph]; }

uint8_t NixieTube::getIntensity(const uint8_t glyph) const {
  if (glyph < cGlyphsPerTube) {
    return _intensity[glyph];
  }

  return _intensity[_activeGlyph];
}

uint32_t NixieTube::getDuration() const { return _duration; }

void NixieTube::adjustIntensity(const uint8_t glyph, const uint16_t scaleFactor) {
  if (glyph < cGlyphsPerTube) {
    uint32_t top = _intensity[glyph] * scaleFactor;
    _intensity[glyph] = top >> 16;
  }
}

void NixieTube::adjustIntensityAll(const uint16_t scaleFactor) {
  for (uint8_t glyph = 0; glyph < NixieTube::cGlyphsPerTube; glyph++) {
    if (_intensity[glyph] > 0) {
      adjustIntensity(glyph, scaleFactor);
    }
  }
}

void NixieTube::lerpToward(uint16_t blendFactor, const NixieTube &target) {
  for (uint8_t i = 0; i < NixieTube::cGlyphsPerTube; i++) {
    int32_t intensity = _intensity[i] - target.getIntensity(i);
    intensity = _intensity[i] - ((intensity * blendFactor) >> 16);
    _intensity[i] = intensity;
  }
}

void NixieTube::setFromLerp(uint16_t blendFactor, const NixieTube &from, const NixieTube &to) {
  for (uint8_t i = 0; i < NixieTube::cGlyphsPerTube; i++) {
    int32_t intensity = from.getIntensity(i) - to.getIntensity(i);
    intensity = from.getIntensity(i) - ((intensity * blendFactor) >> 16);
    _intensity[i] = intensity;
  }
}

}  // namespace kbxTubeClock
