kbx81/TubeClock/src/v1/Keys.h

//
// kbx81's tube clock keys class
// ---------------------------------------------------------------------------
// (c)2019 by kbx81. See LICENSE for details.
//
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

// This class provides access to the touch keys on the device.
//
// This implements a simple key handling mechanism for single key
// presses. If two keys are pressed simultaneously, always the key with the
// higher priority (lower scan code) is used.
//
// Pressed keys are added to a queue, so the code can get all key presses
// even after a short delay.
//
// There is a repeat function enabled, so after ~1s, the pressed key
// is automatically repeated to allow simple interfaces to adjust time/date
// and similar things.
//
#pragma once

#include <cstdint>
#include <string.h>
#include "Hardware.h"

namespace kbxTubeClock::Keys {

// key scan codes
//
enum Key : uint8_t {
  None = 0,
  A = (1 << 5),
  B = (1 << 4),
  C = (1 << 3),
  E = (1 << 2),
  D = (1 << 1),
  U = (1 << 0),
  Power = (1 << 6)  // IR-only: toggles HV power supply
};

// Check the keys
//
void scanKeys();

// Should be called at consistent intervals to insert key repeats
//
void repeatHandler();

// Check if there is a key press in the queue
//
bool hasKeyPress();

// Get the next key from the queue
//
Key getKeyPress();

}  // namespace kbxTubeClock::Keys
