kbx81/TubeClock/src/v1/SerialRemote.h

//
// kbx81's tube clock serial remote control interface
// ---------------------------------------------------------------------------
// (c)2019 by kbx81. See LICENSE for details.
//
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
#pragma once

#include <cstdint>

namespace kbxTubeClock::SerialRemote {

/// @brief Initialize the serial remote control interface
///
void initialize();

/// @brief Called from USART RX interrupt to process incoming bytes
/// @param usart The USART peripheral base address that triggered the interrupt
///
void rxIsr(uint32_t usart);

/// @brief Process a single received byte (e.g. from USB CDC-ACM)
/// @param c The received character
///
void rxByte(char c);

/// @brief Called from USART TX interrupt to send next byte
/// @param usart The USART peripheral base address that triggered the interrupt
///
void txIsr(uint32_t usart);

/// @brief Check if a complete command has been received and is ready to process
/// @return true if a command is ready
///
bool hasCommand();

/// @brief Process a pending command (called from main loop)
///
void process();

/// @brief Notify the remote of a display mode change
/// @param mode The new operating mode
/// @param viewMode The new view sub-mode
///
void notifyModeChange(uint8_t mode, uint8_t viewMode);

/// @brief Notify the remote of a key event
/// @param keyMask Full bitmask of all currently pressed keys (all 6 bits); 0 means all released
///
void notifyKeyEvent(uint8_t keyMask);

/// @brief Notify the remote that the HV supply state was changed via the local UI
///
void notifyHvStateChanged();

/// @brief Notify the remote that a numbered setting was changed via the local UI
/// @param settingNum The setting index (0 – DmxAddress) that changed
///
void notifySettingChanged(uint8_t settingNum);

}  // namespace kbxTubeClock::SerialRemote
