kbx81/TubeClock/src/v1/version.h

#pragma once

// Calendar-based versioning: YY.MM.patch
//   Major = 2-digit year, Minor = month (1–12, NO leading zero — avoids octal literals),
//   Patch = sequential release within the month (also no leading zero).
// Build number increments automatically at compile time (see scripts/bump_build.sh)
// and resets when major (year) or minor (month) changes.
#define FIRMWARE_VERSION_MAJOR 26
#define FIRMWARE_VERSION_MINOR 3
#define FIRMWARE_VERSION_PATCH 1
